bootloop-chris/crmx-bridge-golioth/crmx-bridge-firmware/main/wifi_manager.cc

#include "wifi_manager.h"
#include "esp_wifi.h"
#include "esp_event.h"
#include "esp_netif.h"
#include "esp_log.h"
#include "nvs_flash.h"
#include "freertos/FreeRTOS.h"
#include "freertos/task.h"
#include "freertos/event_groups.h"
#include <cstring>

static const char* TAG = "wifi_manager";

/* FreeRTOS event group to signal when we are connected*/
static EventGroupHandle_t s_wifi_event_group;

/* The event group allows multiple bits for each event, but we only care about two events:
 * - we are connected to the AP with an IP
 * - we failed to connect after the maximum amount of retries */
#define WIFI_CONNECTED_BIT BIT0
#define WIFI_FAIL_BIT      BIT1

#define ESP_MAXIMUM_RETRY  5

static int s_retry_num = 0;
static bool s_initialized = false;

static void event_handler(void* arg, esp_event_base_t event_base,
                         int32_t event_id, void* event_data)
{
    if (event_base == WIFI_EVENT && event_id == WIFI_EVENT_STA_START) {
        esp_wifi_connect();
    } else if (event_base == WIFI_EVENT && event_id == WIFI_EVENT_STA_DISCONNECTED) {
        if (s_retry_num < ESP_MAXIMUM_RETRY) {
            esp_wifi_connect();
            s_retry_num++;
            ESP_LOGI(TAG, "retry to connect to the AP");
        } else {
            xEventGroupSetBits(s_wifi_event_group, WIFI_FAIL_BIT);
        }
        ESP_LOGI(TAG,"connect to the AP fail");
    } else if (event_base == IP_EVENT && event_id == IP_EVENT_STA_GOT_IP) {
        ip_event_got_ip_t* event = (ip_event_got_ip_t*) event_data;
        ESP_LOGI(TAG, "got ip:" IPSTR, IP2STR(&event->ip_info.ip));
        s_retry_num = 0;
        xEventGroupSetBits(s_wifi_event_group, WIFI_CONNECTED_BIT);
    }
}

esp_err_t wifi_manager_init(void)
{
    if (s_initialized) {
        return ESP_OK;
    }

    s_wifi_event_group = xEventGroupCreate();

    ESP_ERROR_CHECK(esp_netif_init());
    ESP_ERROR_CHECK(esp_event_loop_create_default());
    esp_netif_create_default_wifi_sta();

    wifi_init_config_t cfg = WIFI_INIT_CONFIG_DEFAULT();
    ESP_ERROR_CHECK(esp_wifi_init(&cfg));

    esp_event_handler_instance_t instance_any_id;
    esp_event_handler_instance_t instance_got_ip;
    ESP_ERROR_CHECK(esp_event_handler_instance_register(WIFI_EVENT,
                                                        ESP_EVENT_ANY_ID,
                                                        &event_handler,
                                                        NULL,
                                                        &instance_any_id));
    ESP_ERROR_CHECK(esp_event_handler_instance_register(IP_EVENT,
                                                        IP_EVENT_STA_GOT_IP,
                                                        &event_handler,
                                                        NULL,
                                                        &instance_got_ip));

    ESP_ERROR_CHECK(esp_wifi_set_mode(WIFI_MODE_STA));

    s_initialized = true;
    ESP_LOGI(TAG, "WiFi manager initialized");
    
    return ESP_OK;
}

esp_err_t wifi_manager_set_credentials(const char* ssid, const char* password)
{
    if (!s_initialized) {
        return ESP_ERR_INVALID_STATE;
    }

    wifi_config_t wifi_config = {};
    strncpy((char*)wifi_config.sta.ssid, ssid, sizeof(wifi_config.sta.ssid) - 1);
    strncpy((char*)wifi_config.sta.password, password, sizeof(wifi_config.sta.password) - 1);
    wifi_config.sta.threshold.authmode = WIFI_AUTH_WPA2_PSK;
    wifi_config.sta.pmf_cfg.capable = true;
    wifi_config.sta.pmf_cfg.required = false;

    ESP_ERROR_CHECK(esp_wifi_set_config(WIFI_IF_STA, &wifi_config));
    
    ESP_LOGI(TAG, "WiFi credentials set for SSID: %s", ssid);
    return ESP_OK;
}

esp_err_t wifi_manager_connect(void)
{
    if (!s_initialized) {
        return ESP_ERR_INVALID_STATE;
    }

    s_retry_num = 0;
    ESP_ERROR_CHECK(esp_wifi_start());
    
    ESP_LOGI(TAG, "Attempting WiFi connection...");
    return ESP_OK;
}

bool wifi_manager_is_connected(void)
{
    if (!s_initialized || s_wifi_event_group == NULL) {
        return false;
    }

    EventBits_t bits = xEventGroupGetBits(s_wifi_event_group);
    return (bits & WIFI_CONNECTED_BIT) != 0;
}

esp_err_t wifi_manager_wait_for_connection(uint32_t timeout_ms)
{
    if (!s_initialized || s_wifi_event_group == NULL) {
        return ESP_ERR_INVALID_STATE;
    }

    TickType_t timeout_ticks = (timeout_ms == 0) ? portMAX_DELAY : pdMS_TO_TICKS(timeout_ms);
    
    EventBits_t bits = xEventGroupWaitBits(s_wifi_event_group,
            WIFI_CONNECTED_BIT | WIFI_FAIL_BIT,
            pdFALSE,
            pdFALSE,
            timeout_ticks);

    if (bits & WIFI_CONNECTED_BIT) {
        ESP_LOGI(TAG, "Connected to WiFi");
        return ESP_OK;
    } else if (bits & WIFI_FAIL_BIT) {
        ESP_LOGI(TAG, "Failed to connect to WiFi");
        return ESP_ERR_WIFI_CONN;
    } else {
        ESP_LOGI(TAG, "WiFi connection timeout");
        return ESP_ERR_TIMEOUT;
    }
}

esp_err_t wifi_manager_get_ip_address(char* ip_str)
{
    if (!wifi_manager_is_connected()) {
        return ESP_ERR_INVALID_STATE;
    }

    esp_netif_t* netif = esp_netif_get_handle_from_ifkey("WIFI_STA_DEF");
    if (netif == NULL) {
        return ESP_ERR_NOT_FOUND;
    }

    esp_netif_ip_info_t ip_info;
    esp_err_t ret = esp_netif_get_ip_info(netif, &ip_info);
    if (ret == ESP_OK) {
        sprintf(ip_str, IPSTR, IP2STR(&ip_info.ip));
    }
    
    return ret;
}
